blueteamvillage/btv_dc32_badge/art/Camera-1-Edge-01.jpg

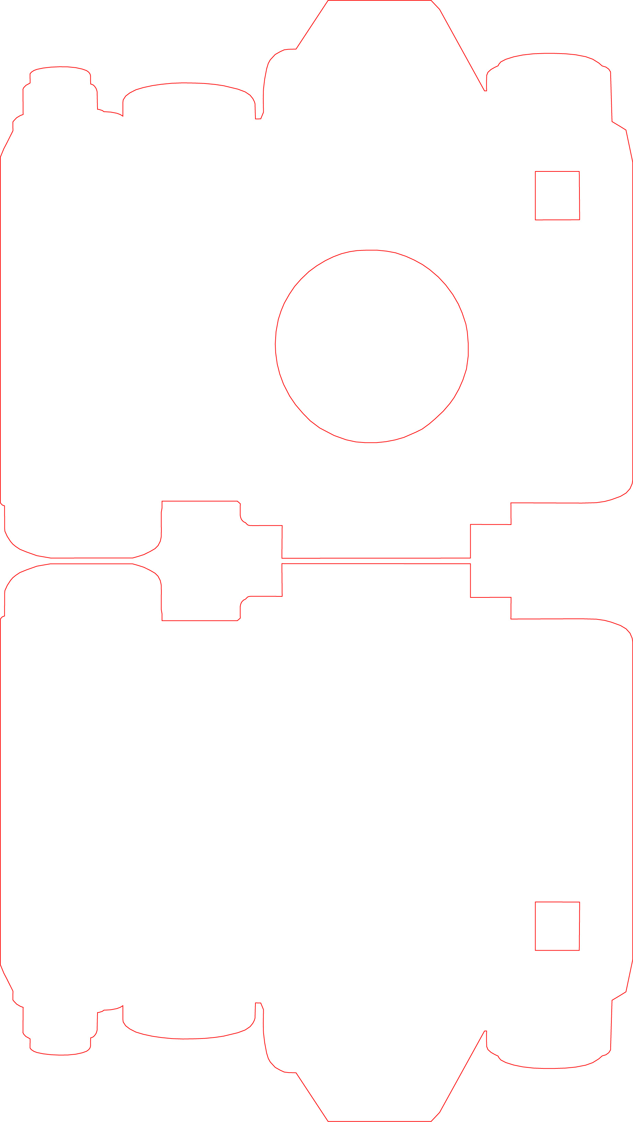
art/Camera-1-Edge-01.jpg
