blueteamvillage/btv_dc32_badge/art/Camera-1-Silk-01.jpg

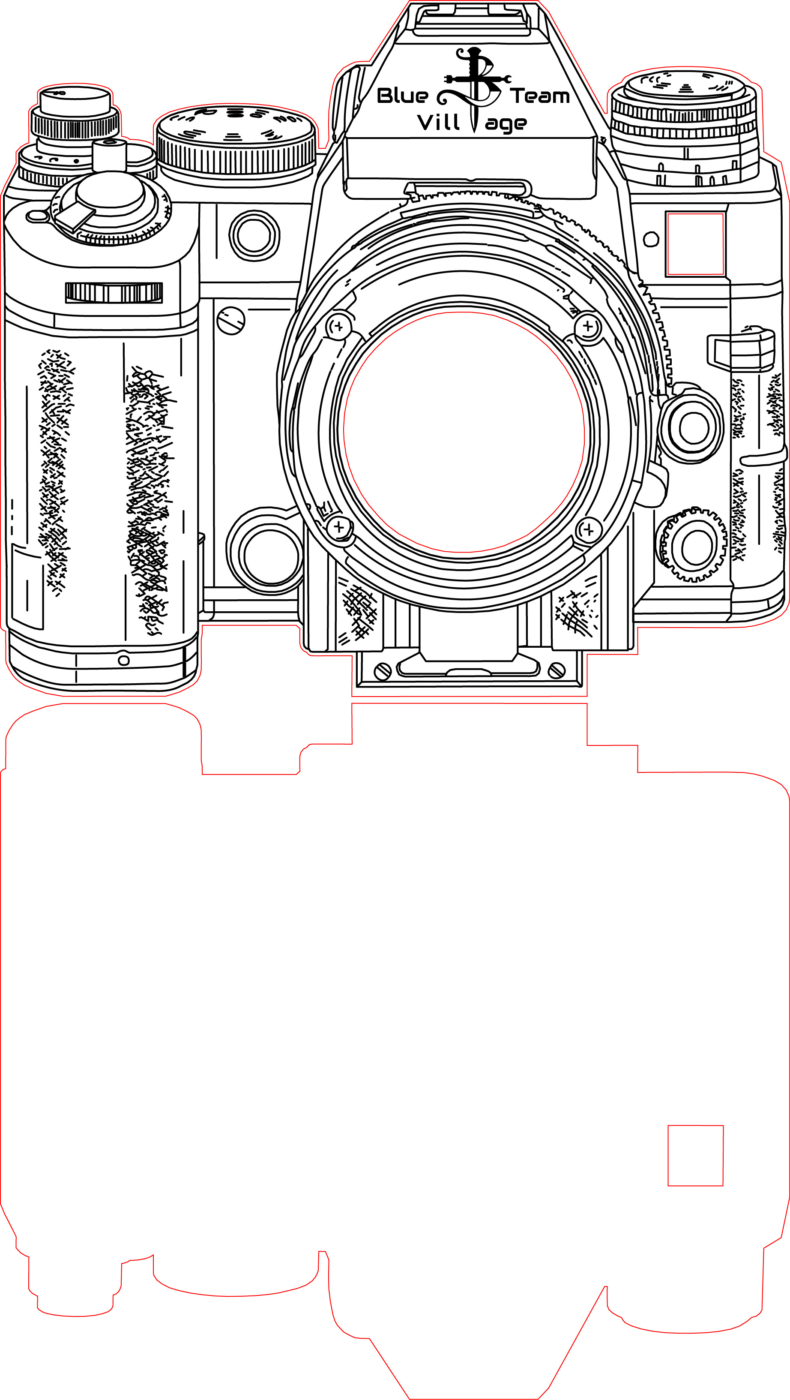
art/Camera-1-Silk-01.jpg
