blueteamvillage/btv_dc32_badge/art/Camera-2-Copper-01.jpg

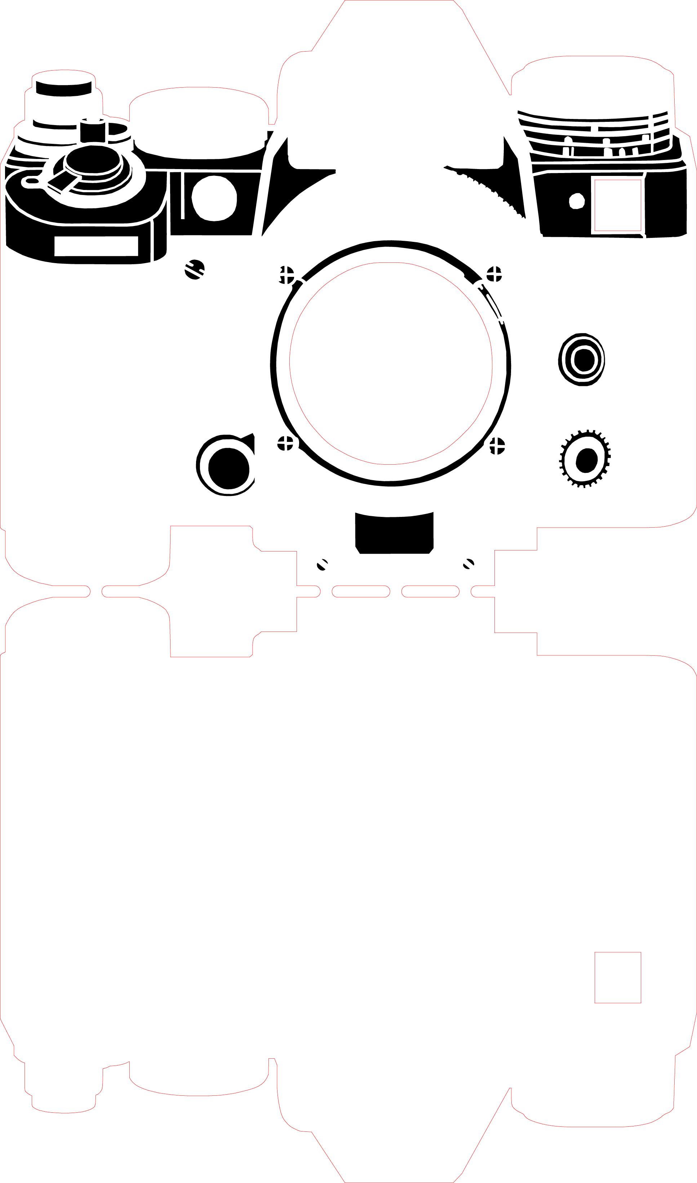
art/Camera-2-Copper-01.jpg
