blueteamvillage/btv_dc32_badge/art/Camera-3-Silk3-01.jpg

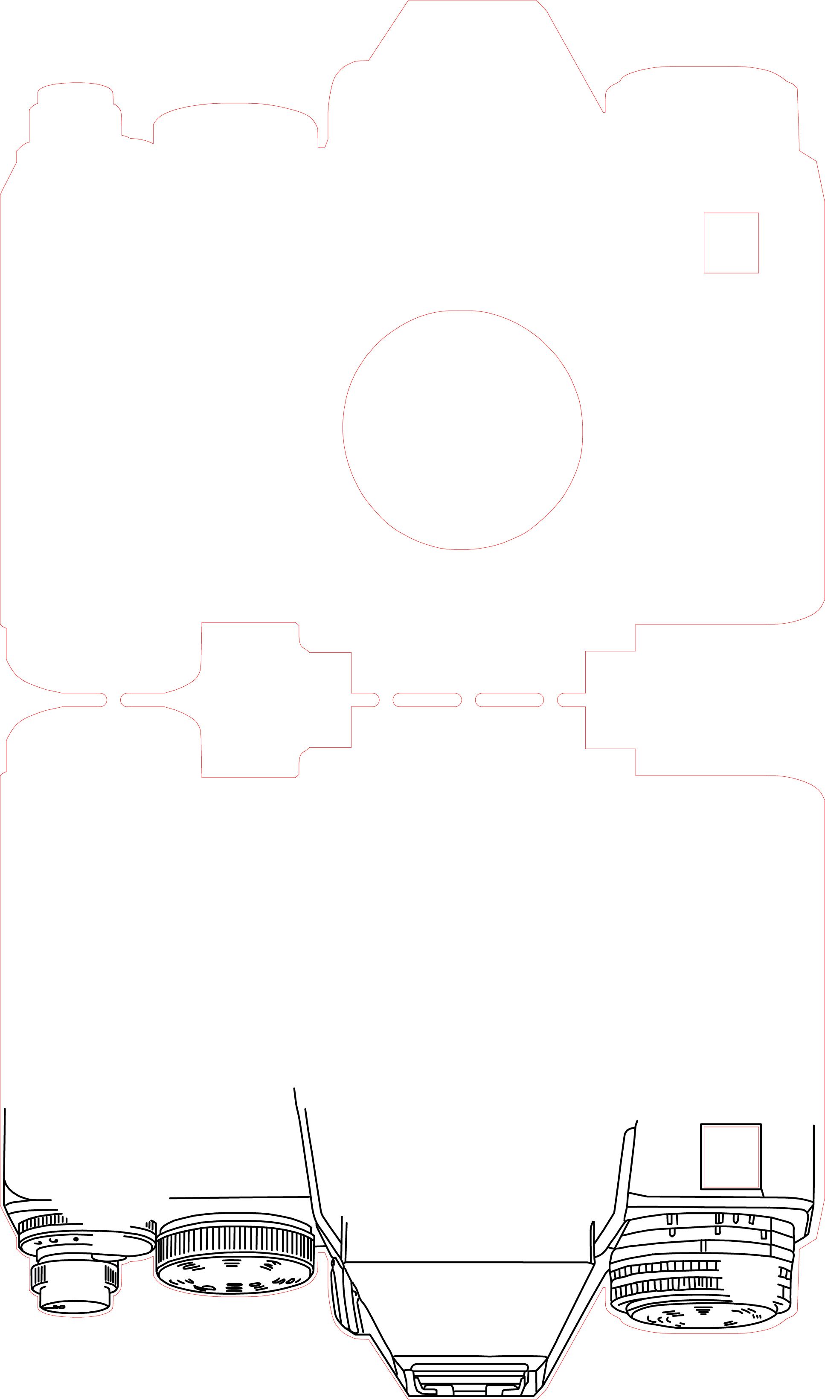
art/Camera-3-Silk3-01.jpg
