blueteamvillage/btv_dc32_badge/art/Camera-4-Silk4-01.jpg

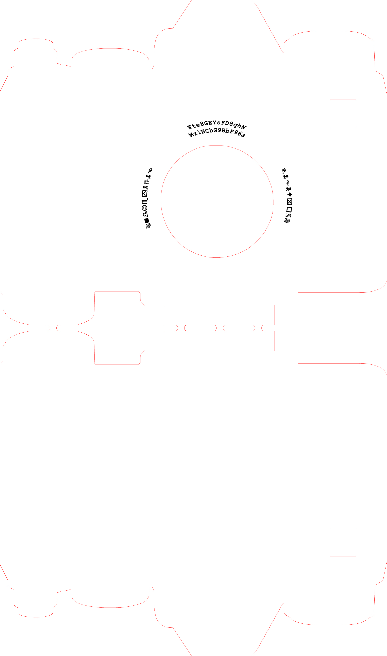
art/Camera-4-Silk4-01.jpg
