blueteamvillage/btv_dc32_badge/art/inspiration/1526_DF_front.webp

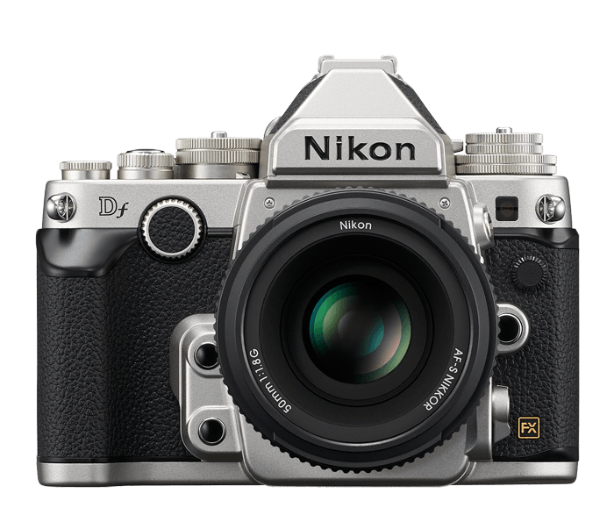
art/inspiration/1526_DF_front.webp
