blueteamvillage/btv_dc32_badge/art/inspiration/alt_bier_steampunk_style_lineart_camera_front_detailed_31d5d3f1-7962-4664-9bf5-ae9651fdb0f0.png

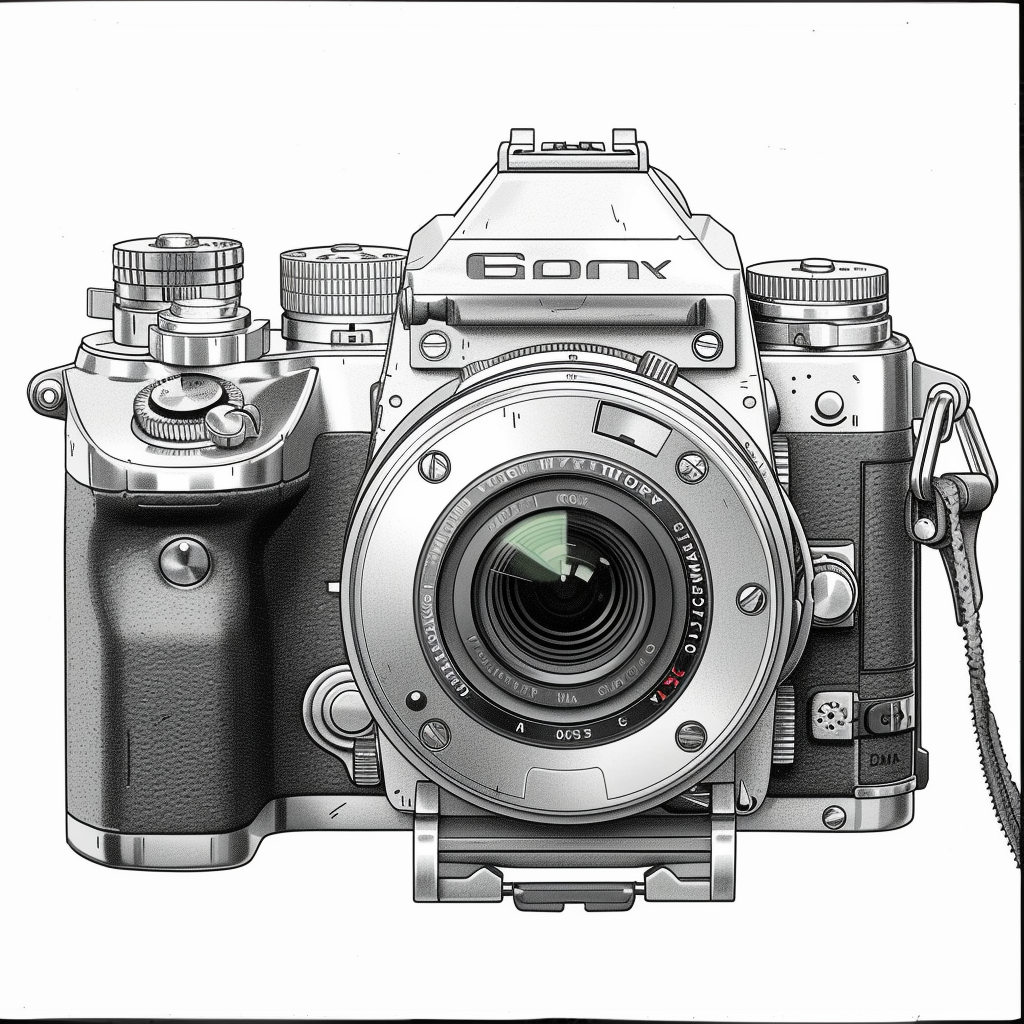
art/inspiration/alt_bier_steampunk_style_lineart_camera_front_detailed_31d5d3f1-7962-4664-9bf5-ae9651fdb0f0.png
