blueteamvillage/btv_dc32_badge/art/inspiration/alt_bier_steampunk_style_lineart_camera_front_detailed_dcd740cc-04af-4e9c-815a-0b84af797cc7.png

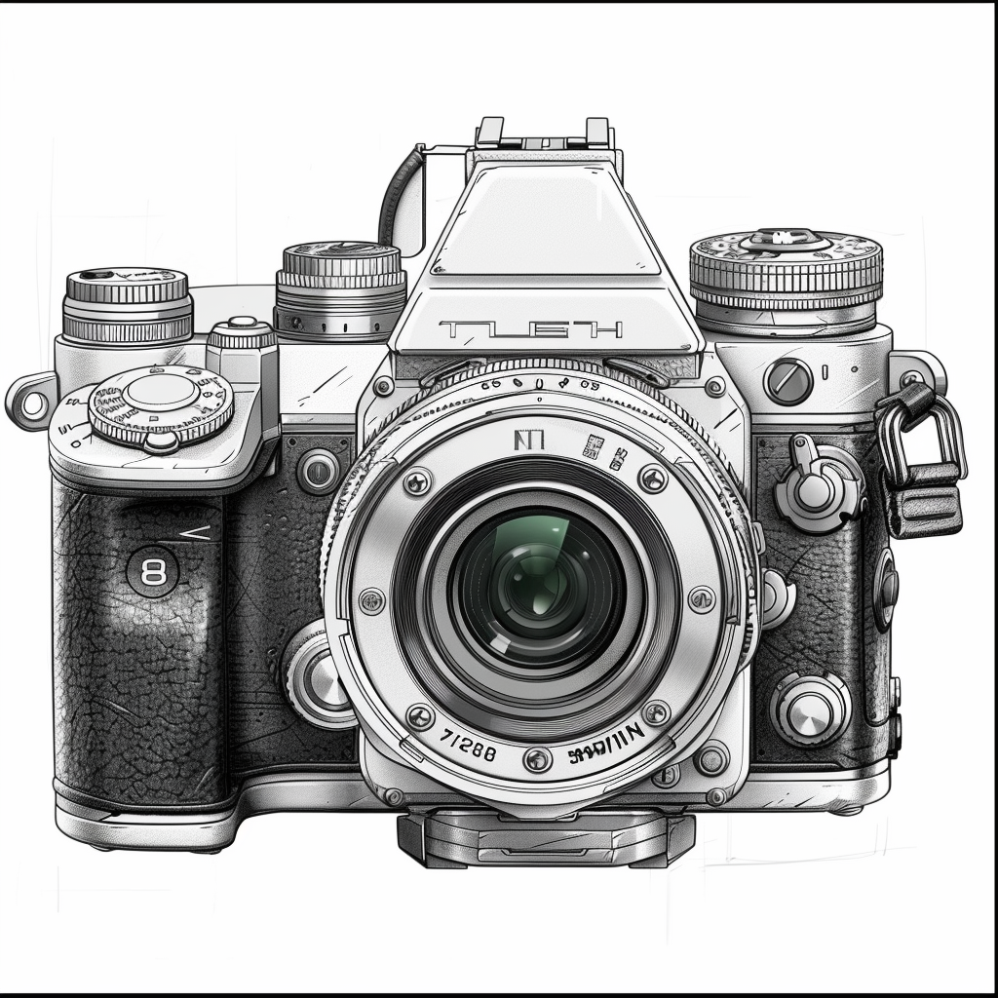
art/inspiration/alt_bier_steampunk_style_lineart_camera_front_detailed_dcd740cc-04af-4e9c-815a-0b84af797cc7.png
