blueteamvillage/btv_dc32_badge/art/inspiration/alt_bier_steampunk_style_lineart_camera_front_detailed_ddf231e1-9c2c-4ddd-9c3d-0c231ffb5367.png

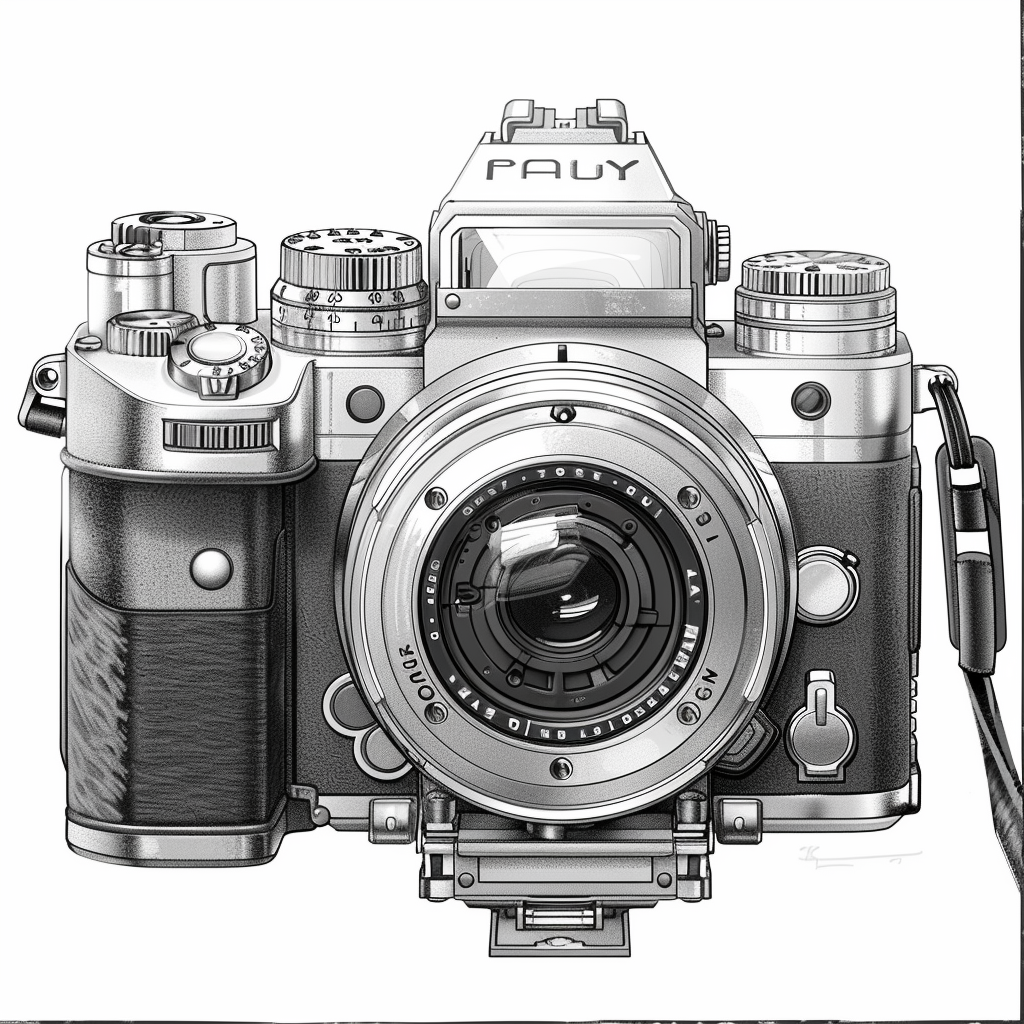
art/inspiration/alt_bier_steampunk_style_lineart_camera_front_detailed_ddf231e1-9c2c-4ddd-9c3d-0c231ffb5367.png
