blueteamvillage/btv_dc32_badge/art/inspiration/camera-with-flashbulb-csa-images.jpg

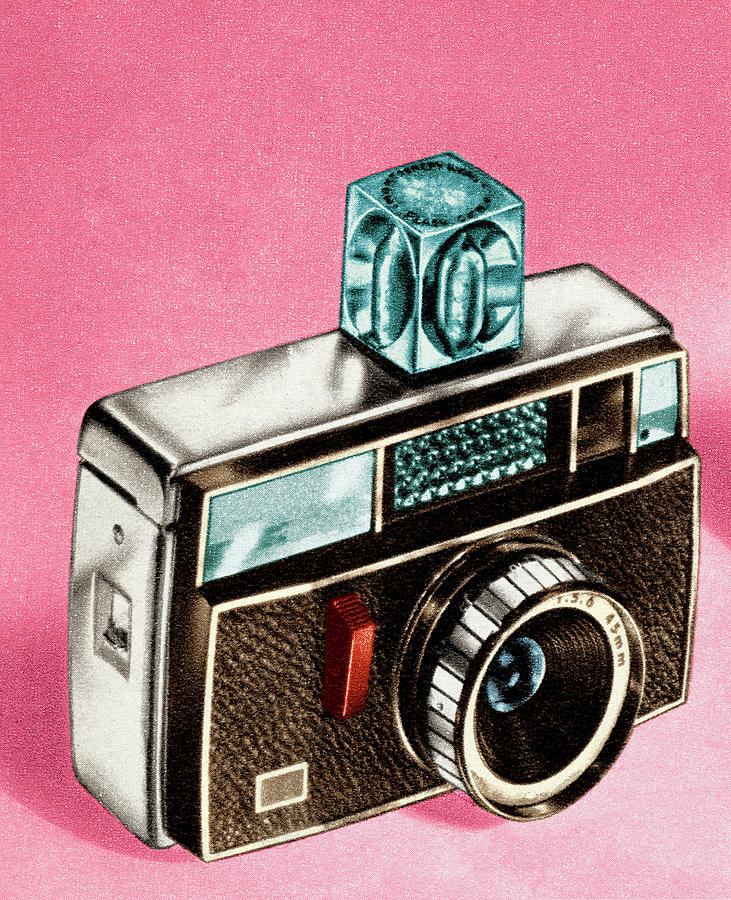
art/inspiration/camera-with-flashbulb-csa-images.jpg
