blueteamvillage/btv_dc32_badge/art/inspiration/il_794xN.4338796224_chcm.webp

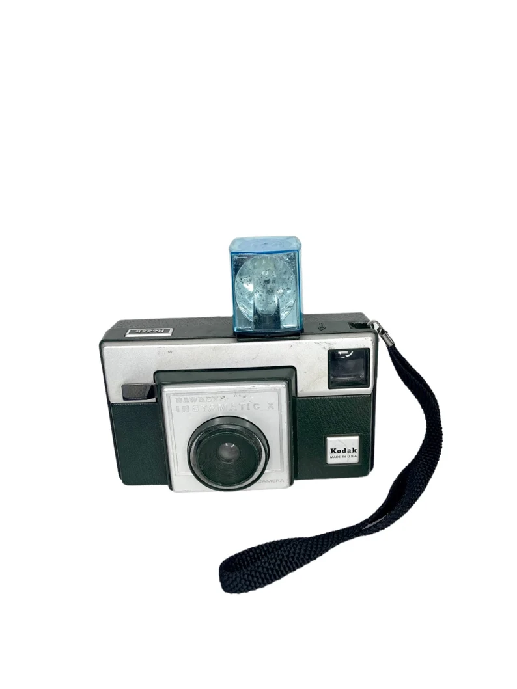
art/inspiration/il_794xN.4338796224_chcm.webp
