blueteamvillage/btv_dc32_badge/art/inspiration/main-qimg-265a1cb40d4eaab294449824ee6765e3-lq.jpeg

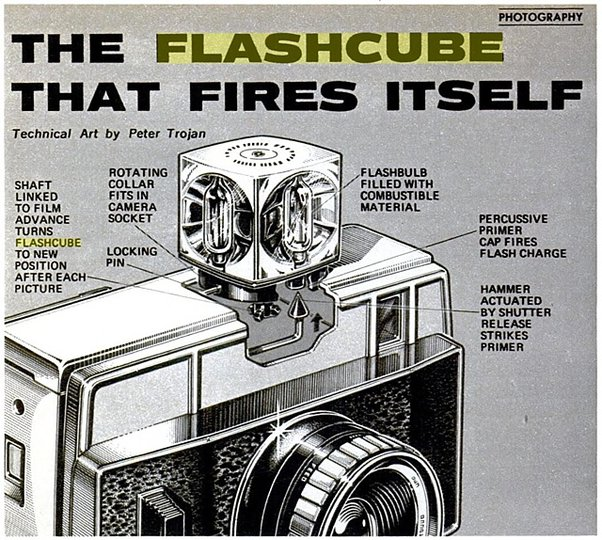
art/inspiration/main-qimg-265a1cb40d4eaab294449824ee6765e3-lq.jpeg
