blueteamvillage/btv_dc32_badge/art/inspiration/nikkon-classic-blk.jpeg

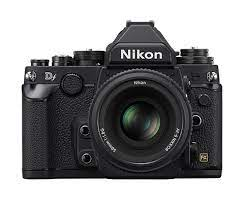
art/inspiration/nikkon-classic-blk.jpeg
