blueteamvillage/btv_dc32_badge/docs/images/ESP32-WeMos-LOLIN32-Lite-pinout-mischianti.png

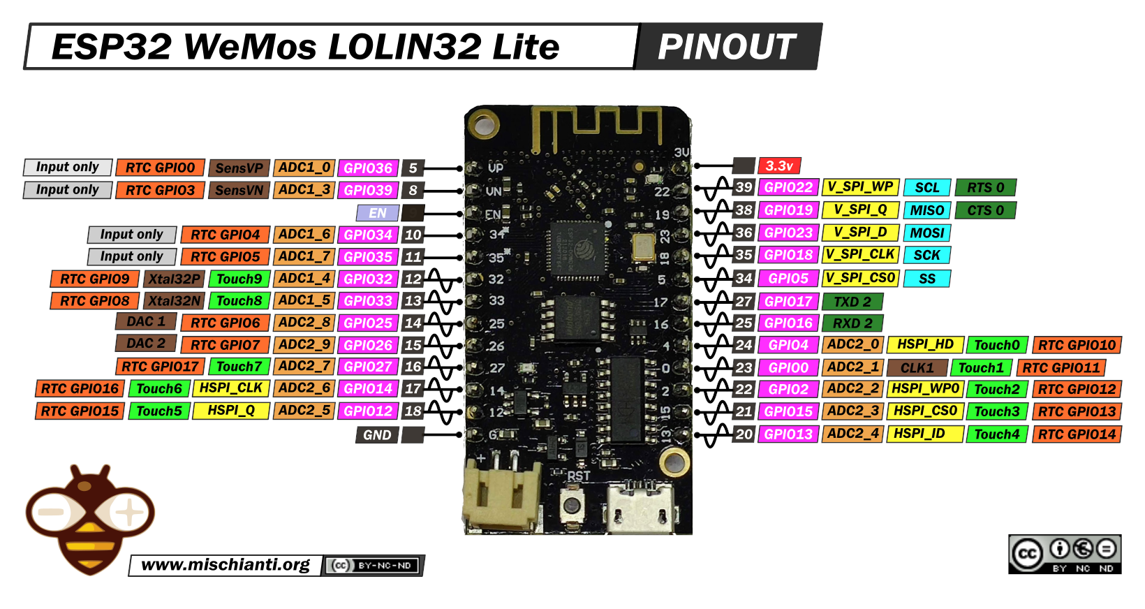
docs/images/ESP32-WeMos-LOLIN32-Lite-pinout-mischianti.png
