blueteamvillage/btv_dc32_badge/eda/camera_badge/3d_models/SW_SS12D00G-Mini-SPDT-Slide-Switch-3pin-1P2T-2-Position-Toggle-Switch-3D.step

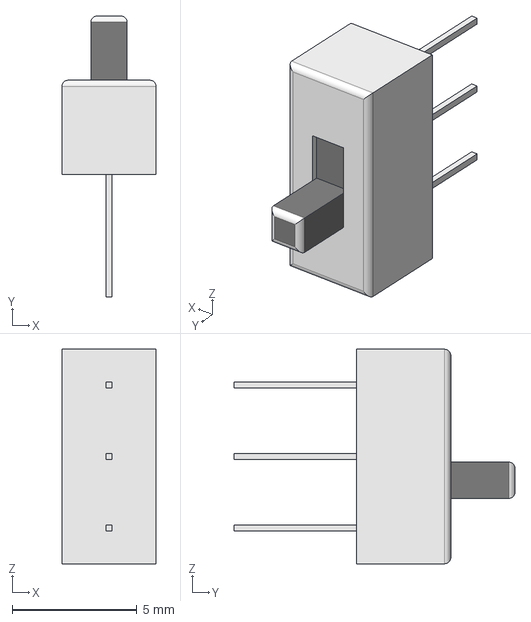
[picture p43: CAD file, 2023-12-28]
eda/camera_badge/3d_models/SW_SS12D00G-Mini-SPDT-Slide-Switch-3pin-1P2T-2-Position-Toggle-Switch-3D.step
3.77 x 11.2 x 8.59 mm
