blueteamvillage/btv_dc32_badge/eda/camera_badge/3d_models/LED_0603_1608Metric.step

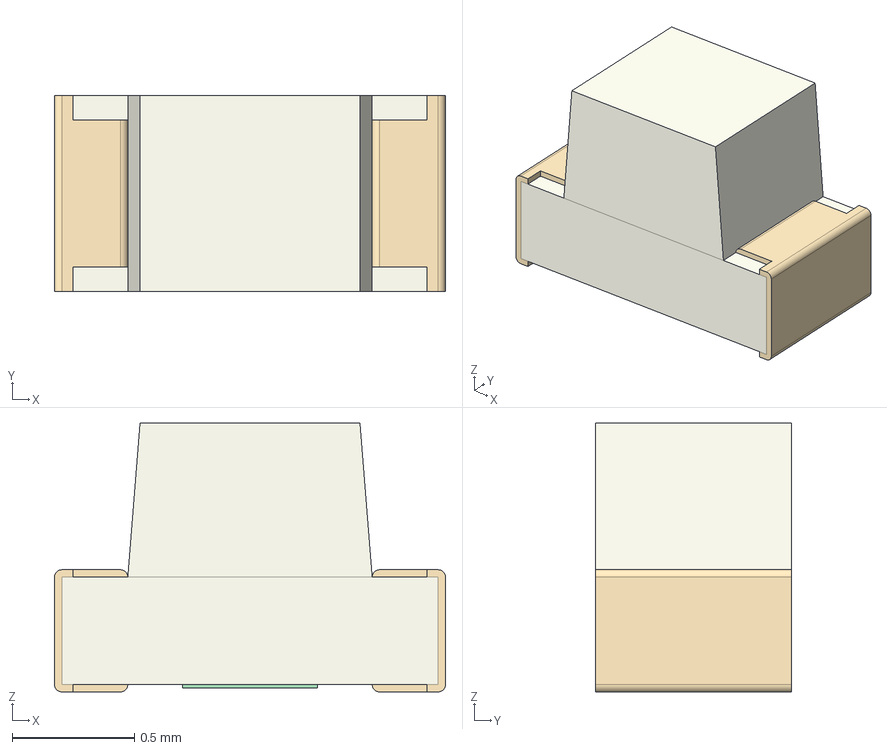
[picture p44: CAD file, 2023-12-28]
eda/camera_badge/3d_models/LED_0603_1608Metric.step
1.60 x 0.8 x 1.10 mm
