blueteamvillage/btv_dc32_badge/eda/camera_badge/3d_models/C_1206_3216Metric.step

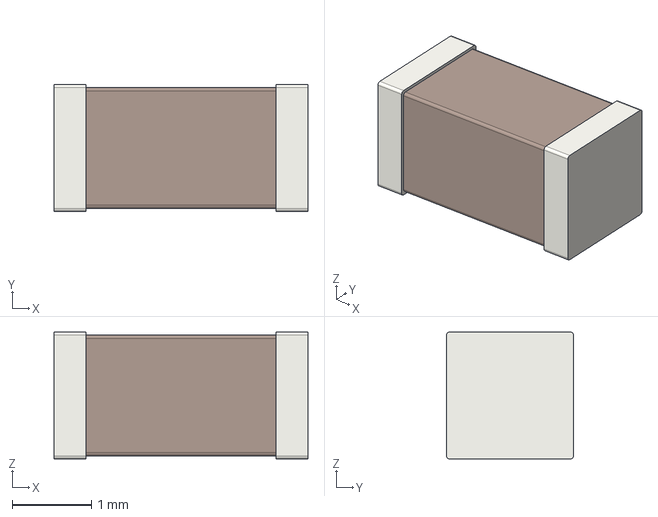
[picture p45: CAD file, 2023-12-28]
eda/camera_badge/3d_models/C_1206_3216Metric.step
3.20 x 1.60 x 1.60 mm
