blueteamvillage/btv_dc32_badge/eda/camera_badge/3d_models/LED_D8.0mm.step

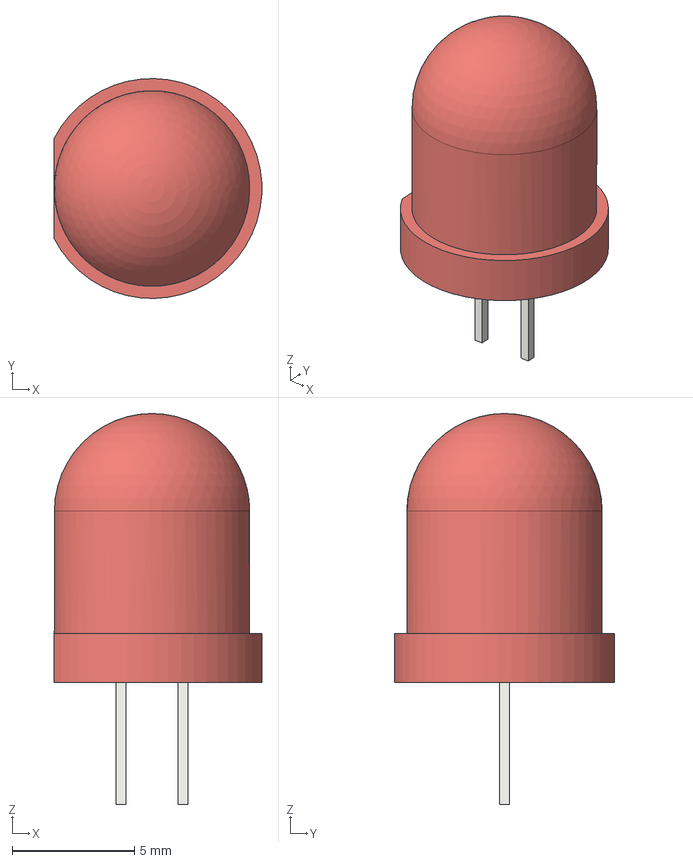
[picture p48: CAD file, 2023-12-28]
eda/camera_badge/3d_models/LED_D8.0mm.step
8.49 x 9.00 x 16.0 mm
