blueteamvillage/btv_dc32_badge/eda/camera_badge/3d_models/PinHeader_1x15_P2.54mm_Vertical.step

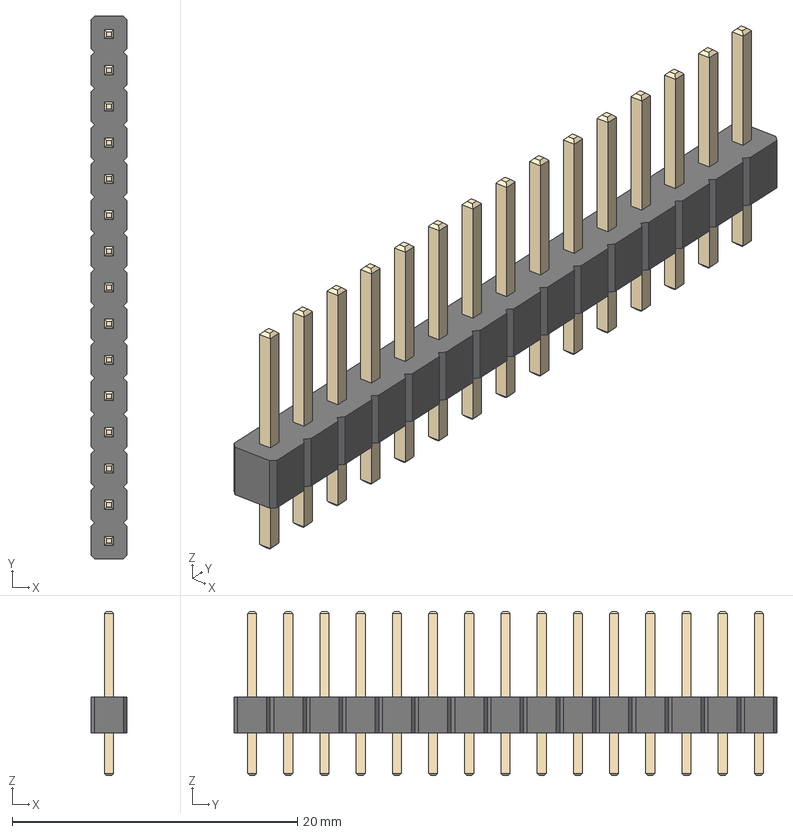
[picture p51: CAD file, 2023-12-28]
eda/camera_badge/3d_models/PinHeader_1x15_P2.54mm_Vertical.step
2.54 x 38.1 x 11.5 mm
