blueteamvillage/btv_dc32_badge/eda/camera_badge/3d_models/CUI_PXO7803-500-M-TR.step

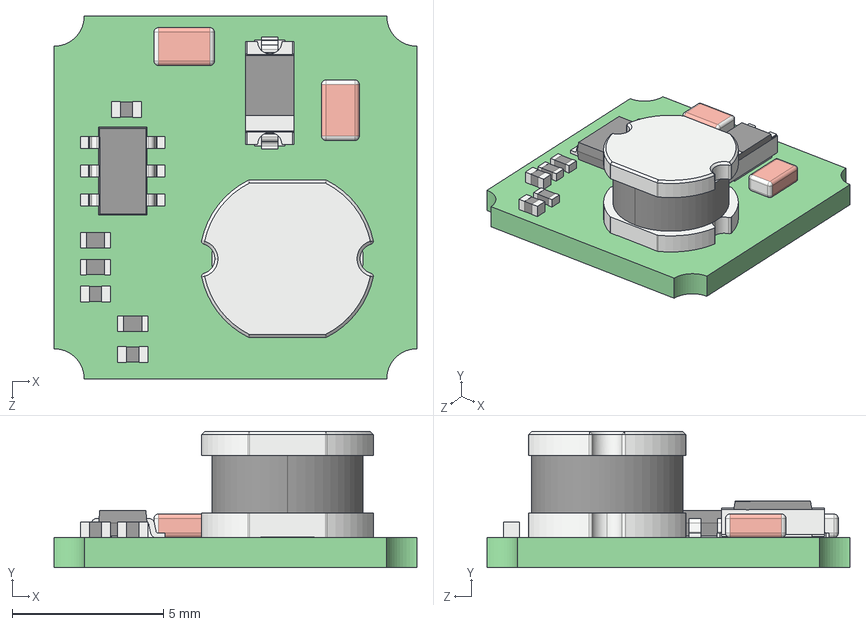
[picture p53: CAD file, 2023-12-28]
eda/camera_badge/3d_models/CUI_PXO7803-500-M-TR.step
12.0 x 4.50 x 12.0 mm
