blueteamvillage/btv_dc32_badge/eda/camera_badge/3d_models/C_Rect_L4.6mm_W2.0mm_P2.50mm_MKS02_FKP02.step

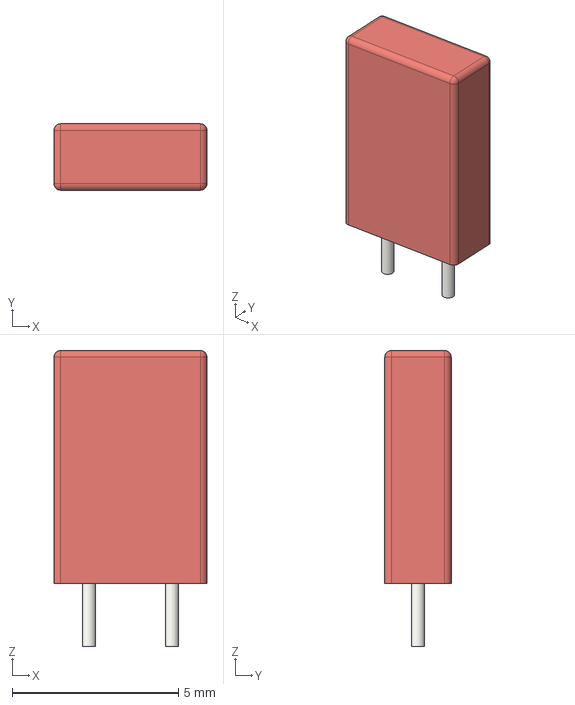
[picture p54: CAD file, 2023-12-28]
eda/camera_badge/3d_models/C_Rect_L4.6mm_W2.0mm_P2.50mm_MKS02_FKP02.step
4.60 x 2.00 x 8.90 mm
