blueteamvillage/btv_dc32_badge/eda/camera_badge/3d_models/TO-92_Inline.step

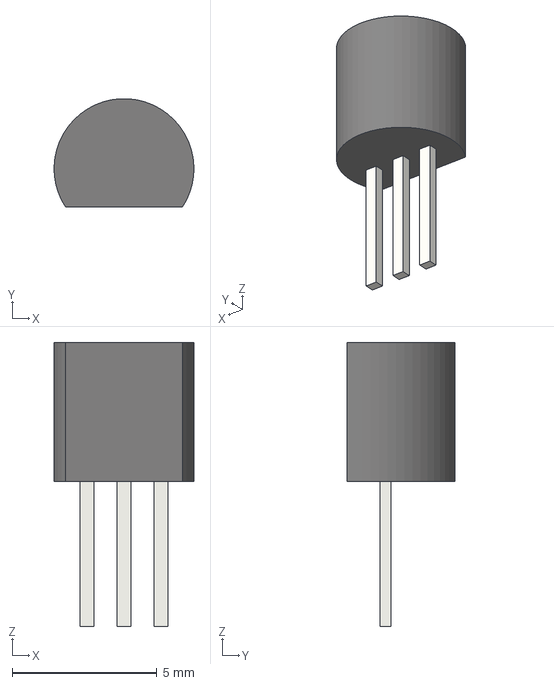
[picture p55: CAD file, 2023-12-28]
eda/camera_badge/3d_models/TO-92_Inline.step
4.83 x 3.74 x 9.80 mm
