blueteamvillage/btv_dc32_badge/eda/camera_badge/3d_models/TS2306A.step

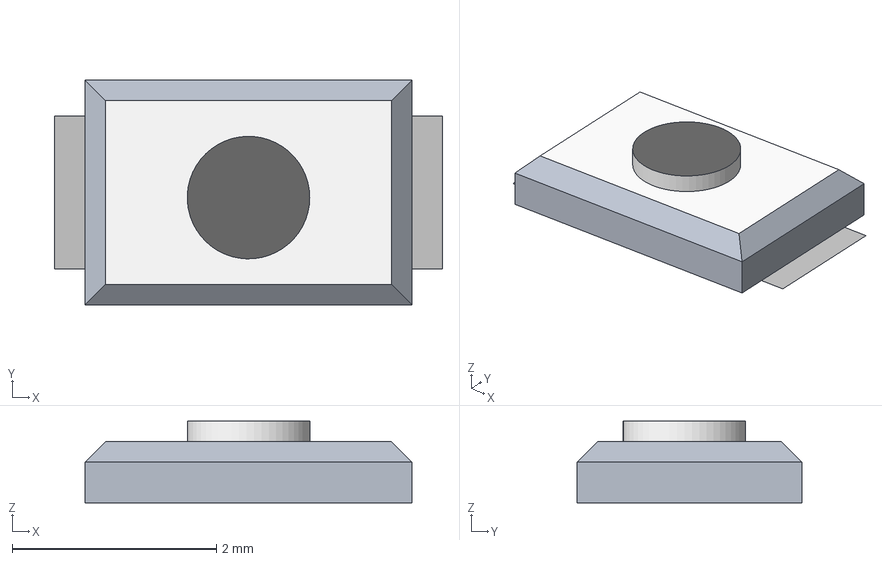
[picture p56: CAD file, 2023-12-28]
eda/camera_badge/3d_models/TS2306A.step
3.80 x 2.20 x 0.8 mm
Plane
