blueteamvillage/btv_dc32_badge/eda/camera_badge/3d_models/BatteryHolder_2466_1xAAA.step

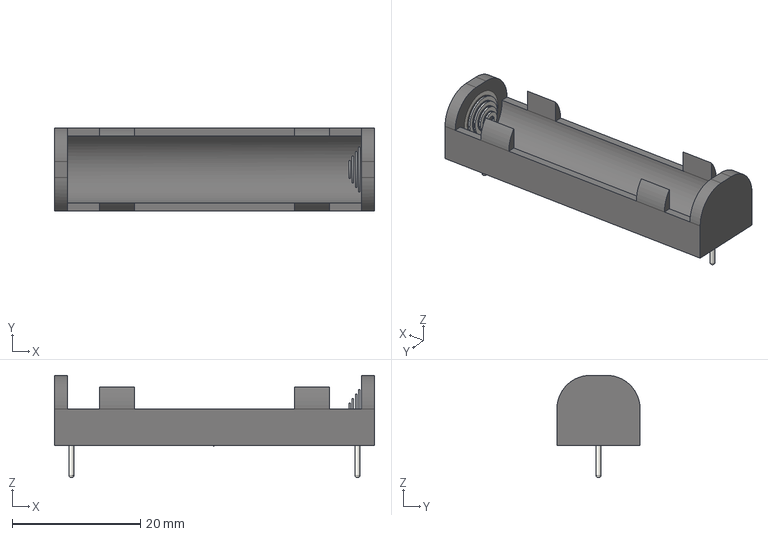
[picture p59: CAD file, 2023-12-28]
eda/camera_badge/3d_models/BatteryHolder_2466_1xAAA.step
50.0 x 13.0 x 16.0 mm
