blueteamvillage/btv_dc32_badge/eda/camera_badge/3d_models/C_Disc_D3.0mm_W2.0mm_P2.50mm.step

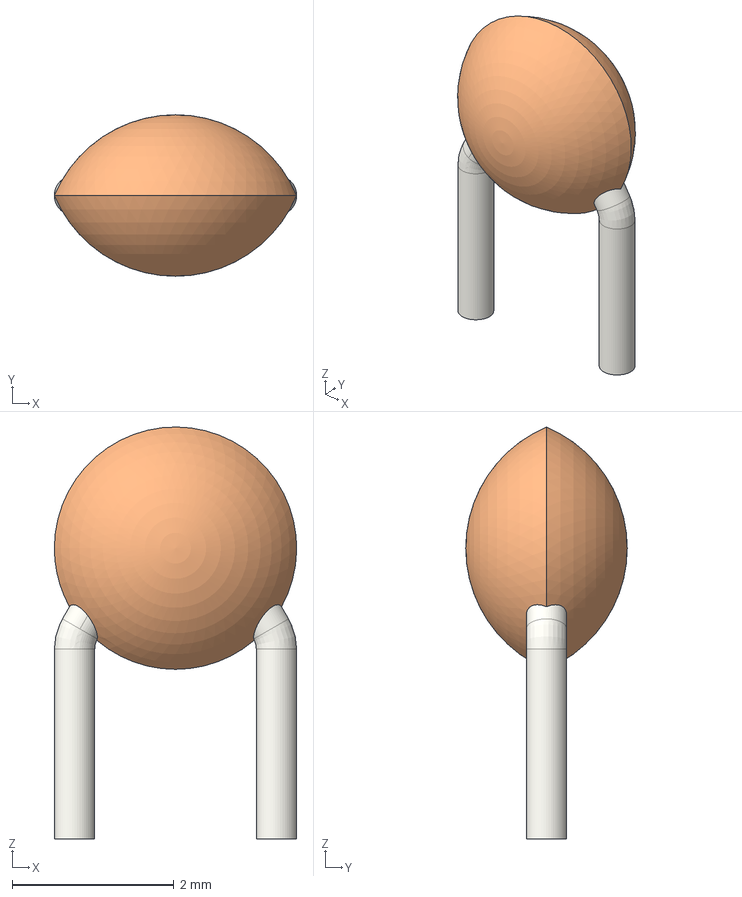
[picture p62: CAD file, 2023-12-28]
eda/camera_badge/3d_models/C_Disc_D3.0mm_W2.0mm_P2.50mm.step
3.00 x 2.00 x 5.10 mm
