blueteamvillage/btv_dc32_badge/eda/camera_badge/3d_models/PinSocket_1x20_P2.54mm_Horizontal.step

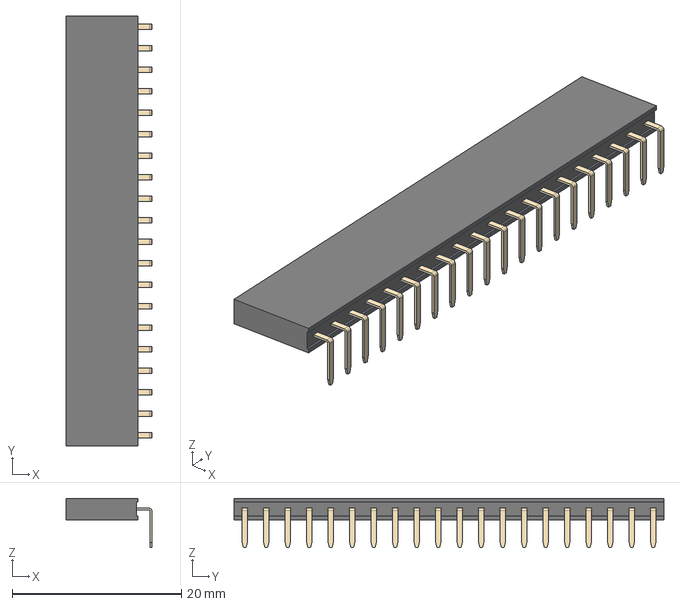
[picture p63: CAD file, 2023-12-28]
eda/camera_badge/3d_models/PinSocket_1x20_P2.54mm_Horizontal.step
10.1 x 50.8 x 5.84 mm
