blueteamvillage/btv_dc32_badge/eda/camera_badge/3d_models/R_1206_3216Metric.step

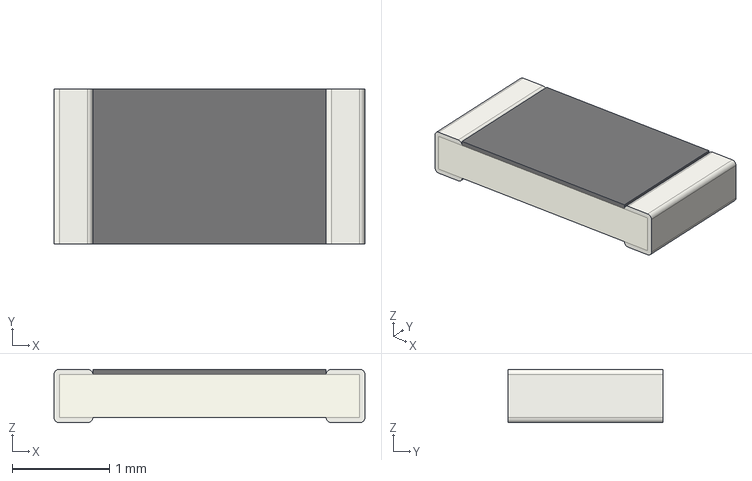
[picture p65: CAD file, 2023-12-28]
eda/camera_badge/3d_models/R_1206_3216Metric.step
3.20 x 1.60 x 0.55 mm
