blueteamvillage/btv_dc32_badge/eda/camera_badge/3d_models/USB_Micro-B_Molex_47346-0001.step

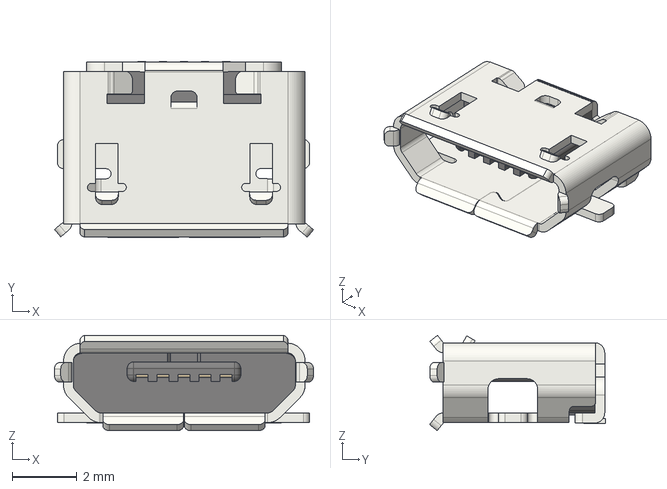
[picture p66: CAD file, 2023-12-28]
eda/camera_badge/3d_models/USB_Micro-B_Molex_47346-0001.step
7.98 x 5.42 x 2.94 mm
