blueteamvillage/btv_dc32_badge/eda/camera_badge/3d_models/PinSocket_1x10_P2.54mm_Horizontal.step

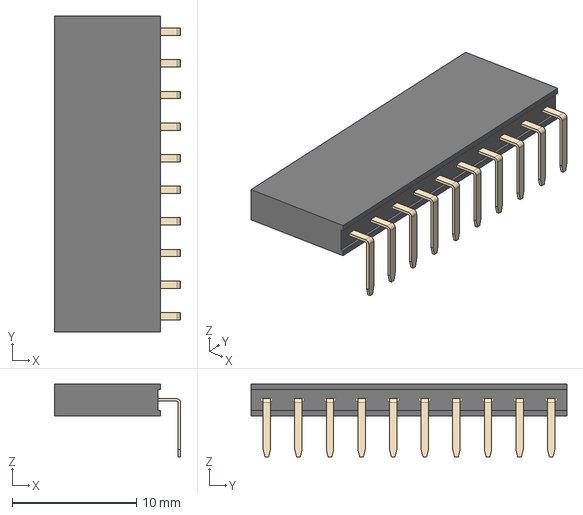
[picture p68: CAD file, 2023-12-28]
eda/camera_badge/3d_models/PinSocket_1x10_P2.54mm_Horizontal.step
10.1 x 25.4 x 5.84 mm
