blueteamvillage/btv_dc32_badge/eda/camera_badge/3d_models/PinSocket_1x10_P2.54mm_Vertical.step

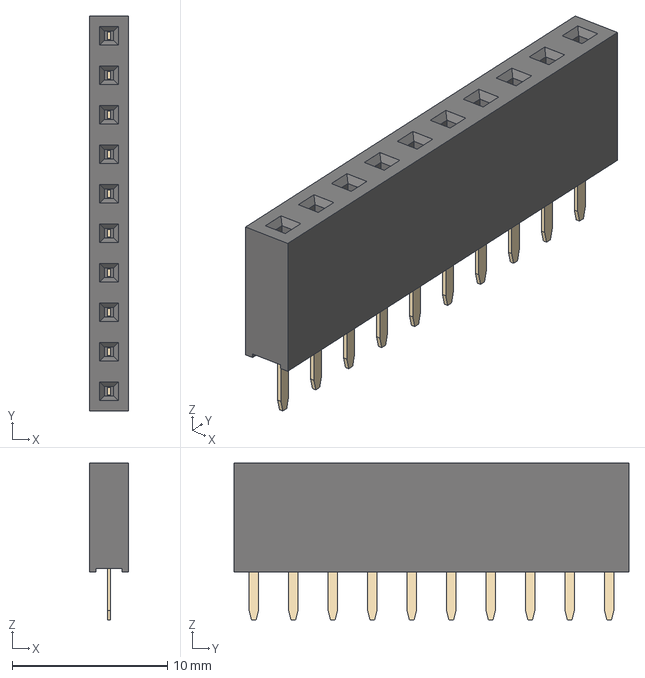
[picture p70: CAD file, 2023-12-28]
eda/camera_badge/3d_models/PinSocket_1x10_P2.54mm_Vertical.step
2.54 x 25.4 x 10.1 mm
