blueteamvillage/btv_dc32_badge/eda/camera_badge/3d_models/Battery_Holder_CR2032_BS-2-1.stp

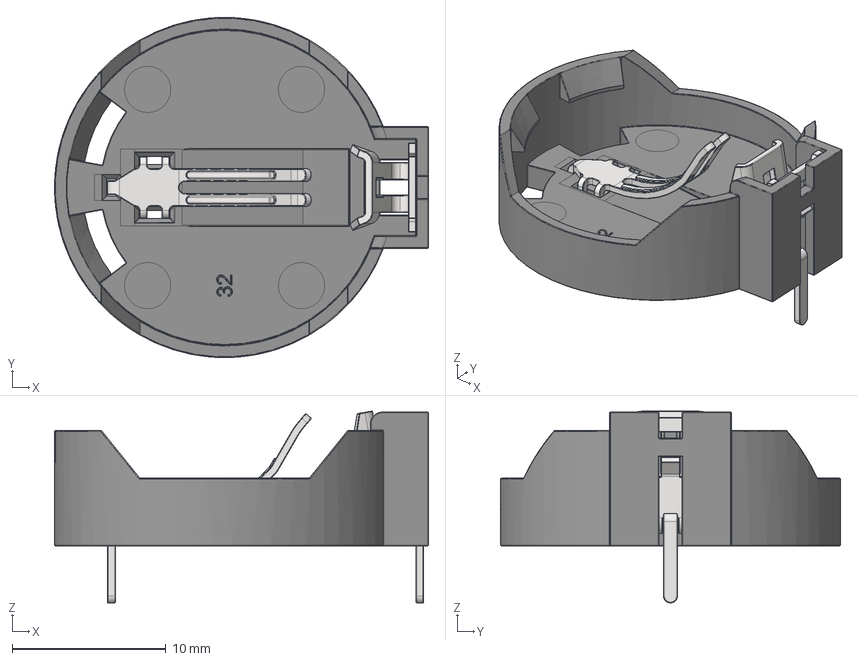
[picture p72: CAD file, 2023-12-28]
eda/camera_badge/3d_models/Battery_Holder_CR2032_BS-2-1.stp
24.3 x 22.1 x 12.5 mm
