blueteamvillage/btv_dc32_badge/eda/camera_badge/3d_models/R_Axial_DIN0207_L6.3mm_D2.5mm_P7.62mm_Horizontal.step

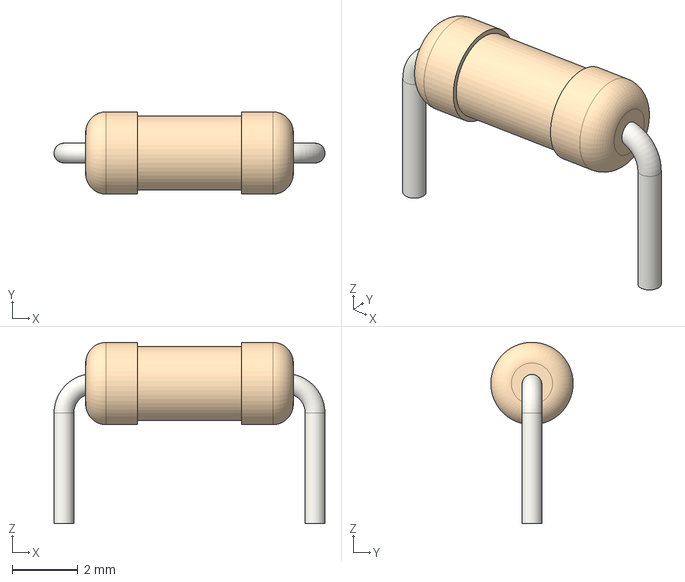
[picture p78: CAD file, 2023-12-28]
eda/camera_badge/3d_models/R_Axial_DIN0207_L6.3mm_D2.5mm_P7.62mm_Horizontal.step
8.22 x 2.50 x 5.50 mm
