blueteamvillage/btv_dc32_badge/eda/camera_badge/3d_models/C_0805_2012Metric.step

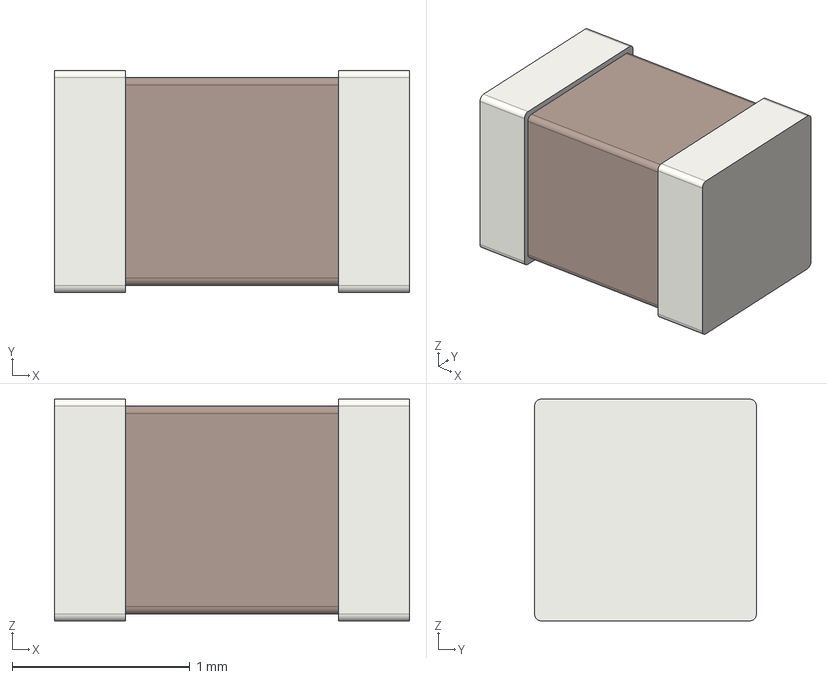
[picture p79: CAD file, 2023-12-28]
eda/camera_badge/3d_models/C_0805_2012Metric.step
2.00 x 1.25 x 1.25 mm
