blueteamvillage/btv_dc32_badge/eda/camera_badge/3d_models/PinSocket_1x05_P2.54mm_Vertical.step

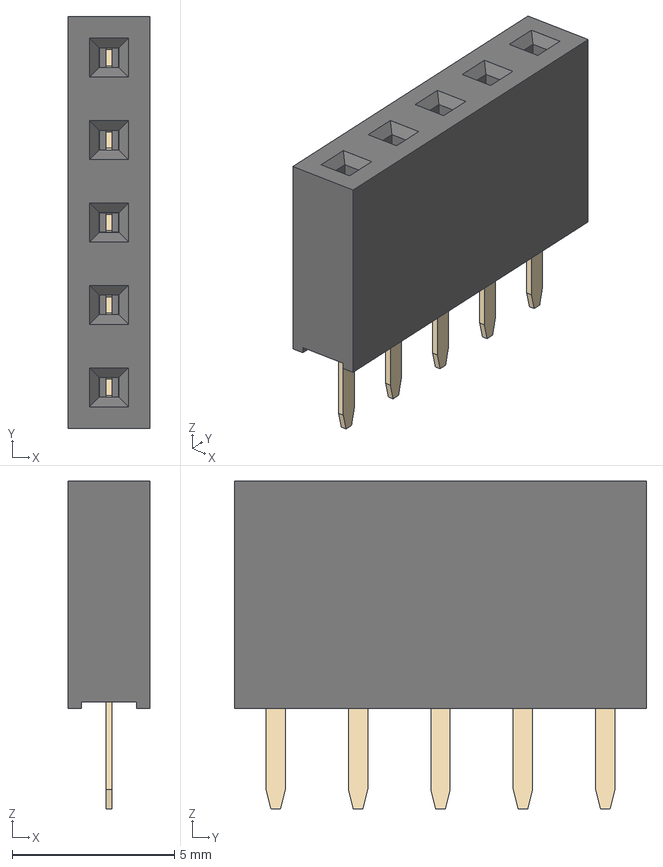
[picture p82: CAD file, 2023-12-28]
eda/camera_badge/3d_models/PinSocket_1x05_P2.54mm_Vertical.step
2.54 x 12.7 x 10.1 mm
