blueteamvillage/btv_dc32_badge/eda/camera_badge/3d_models/RJ45_Amphenol_RJHSE538X.step

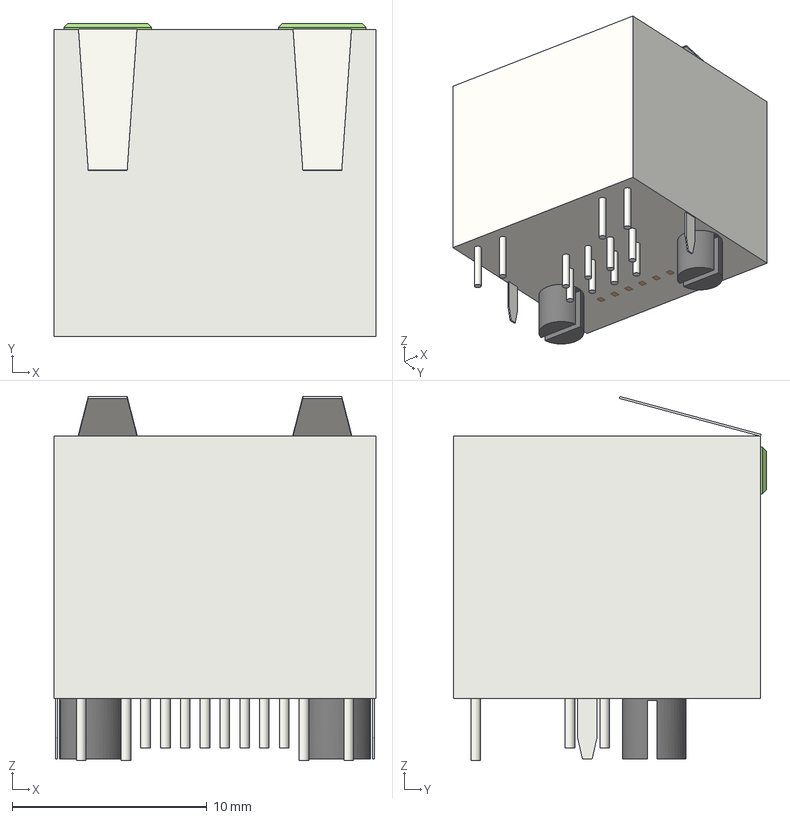
[picture p83: CAD file, 2023-12-28]
eda/camera_badge/3d_models/RJ45_Amphenol_RJHSE538X.step
16.5 x 16.1 x 18.7 mm
