blueteamvillage/btv_dc32_badge/eda/camera_badge/3d_models/RJ45_Amphenol_RJHSE-5080-56544.STEP

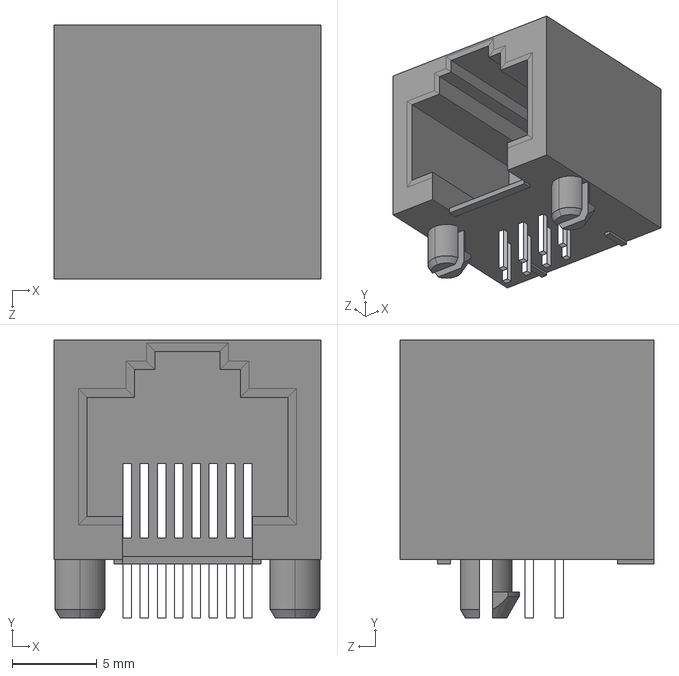
[picture p84: CAD file, 2023-12-28]
eda/camera_badge/3d_models/RJ45_Amphenol_RJHSE-5080-56544.STEP
15.7 x 16.4 x 15.0 mm
