blueteamvillage/btv_dc32_badge/eda/camera_badge/3d_models/R_0603_1608Metric.step

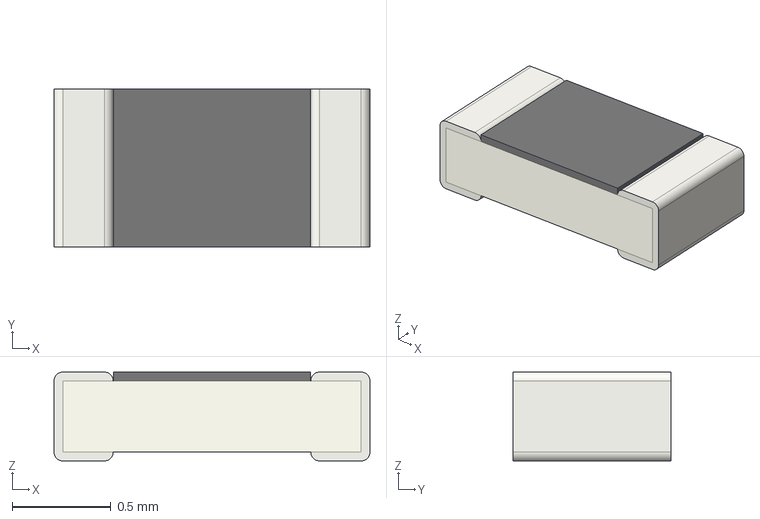
[picture p88: CAD file, 2023-12-28]
eda/camera_badge/3d_models/R_0603_1608Metric.step
1.60 x 0.8 x 0.45 mm
