blueteamvillage/btv_dc32_badge/eda/camera_badge/3d_models/PinHeader_1x01_P2.54mm_Horizontal.step

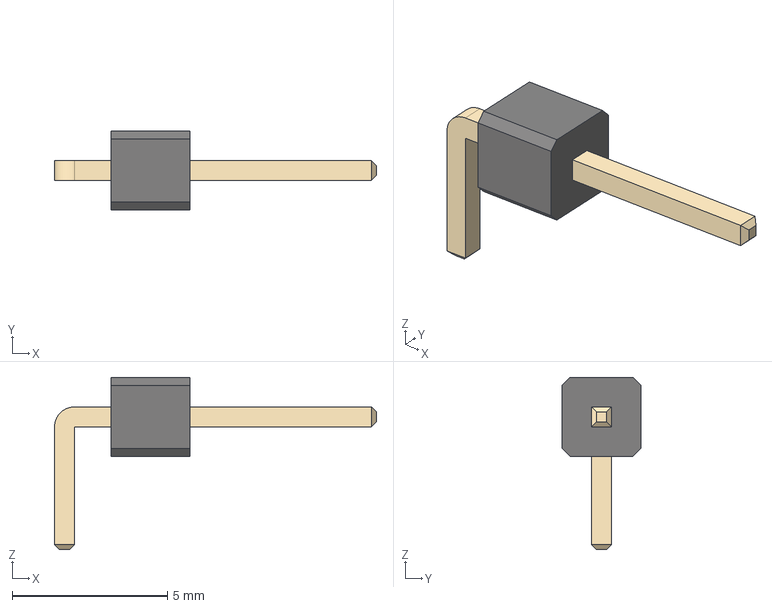
[picture p90: CAD file, 2023-12-28]
eda/camera_badge/3d_models/PinHeader_1x01_P2.54mm_Horizontal.step
10.4 x 2.54 x 5.54 mm
