blueteamvillage/btv_dc32_badge/eda/camera_badge/3d_models/BatteryHolder_2468_2xAAA.step

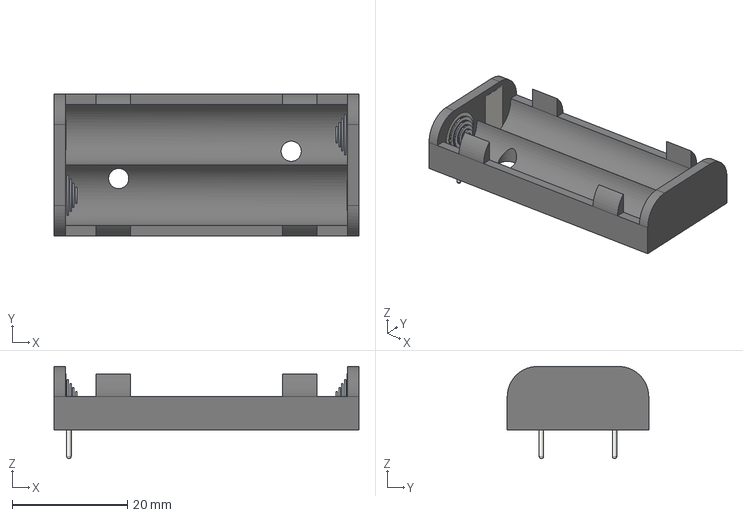
[picture p91: CAD file, 2023-12-28]
eda/camera_badge/3d_models/BatteryHolder_2468_2xAAA.step
53.0 x 24.6 x 16.0 mm
