blueteamvillage/btv_dc32_badge/eda/camera_badge/3d_models/SOT-23.step

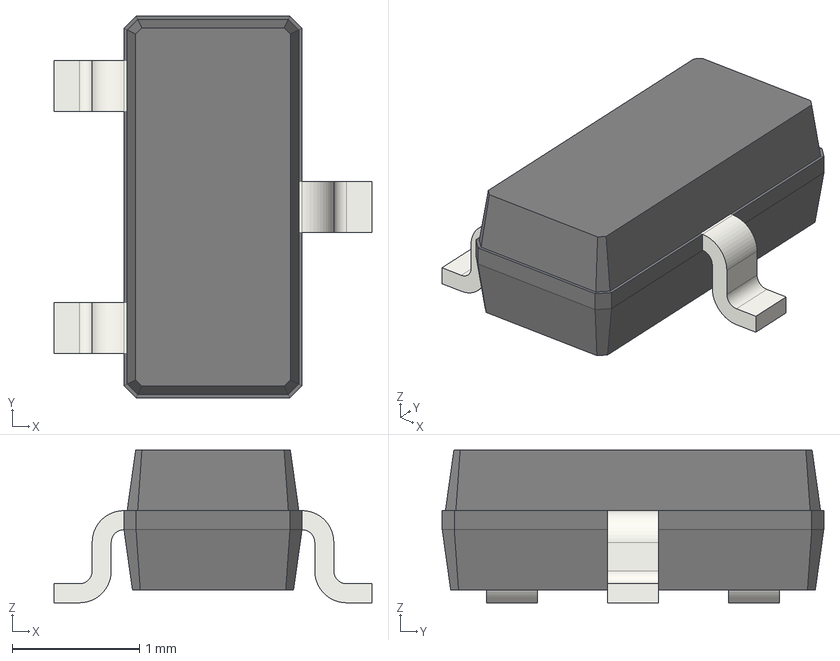
[picture p92: CAD file, 2023-12-28]
eda/camera_badge/3d_models/SOT-23.step
2.50 x 3.00 x 1.20 mm
