blueteamvillage/btv_dc32_badge/eda/camera_badge/3d_models/LED_D5.0mm.step

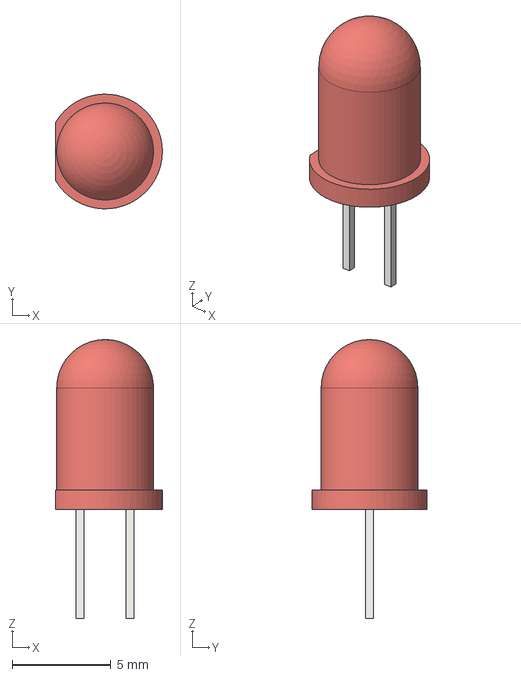
[picture p95: CAD file, 2023-12-28]
eda/camera_badge/3d_models/LED_D5.0mm.step
5.40 x 5.79 x 14.1 mm
