blueteamvillage/btv_dc32_badge/eda/camera_badge/3d_models/Battery_Holder_3xAAA_Simple.step

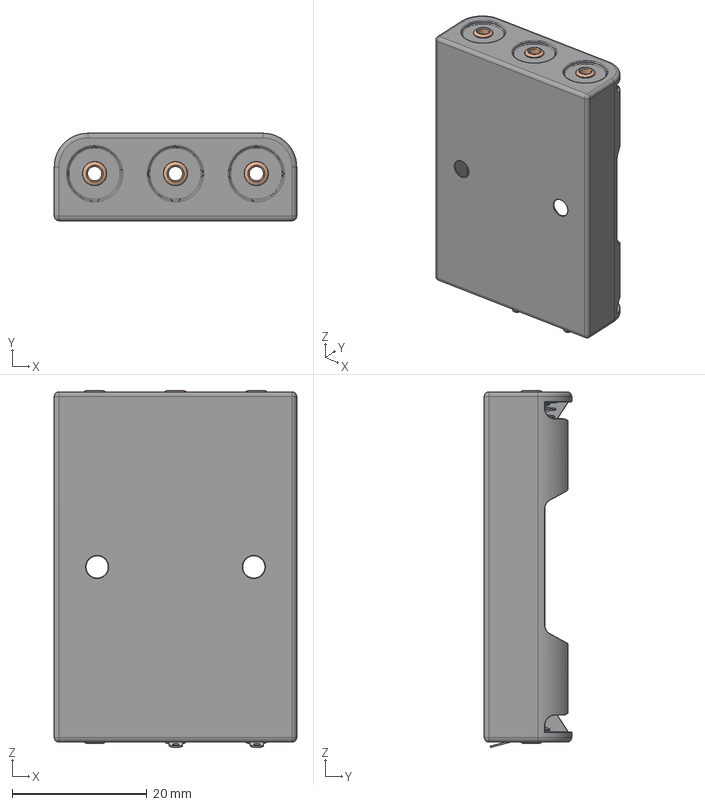
[picture p97: CAD file, 2023-12-28]
eda/camera_badge/3d_models/Battery_Holder_3xAAA_Simple.step
36.0 x 13.0 x 53.0 mm
