blueteamvillage/btv_dc32_badge/eda/camera_badge/3d_models/LED_D3.0mm-3.step

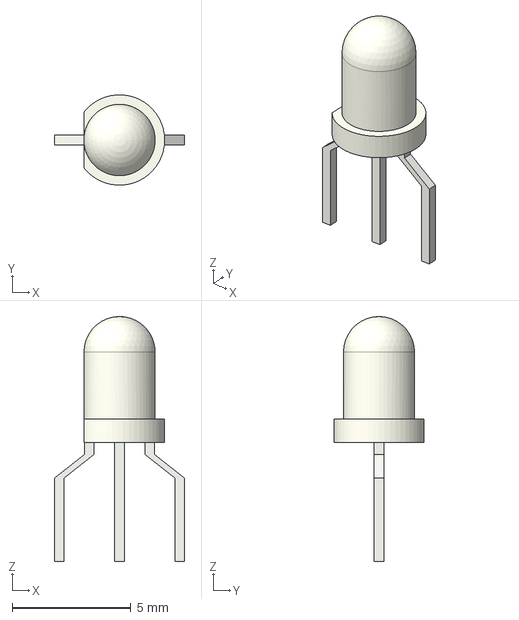
[picture p102: CAD file, 2023-12-28]
eda/camera_badge/3d_models/LED_D3.0mm-3.step
5.48 x 3.80 x 10.3 mm
