blueteamvillage/btv_dc32_badge/eda/camera_badge/3d_models/CP_Radial_D6.3mm_P2.50mm.step

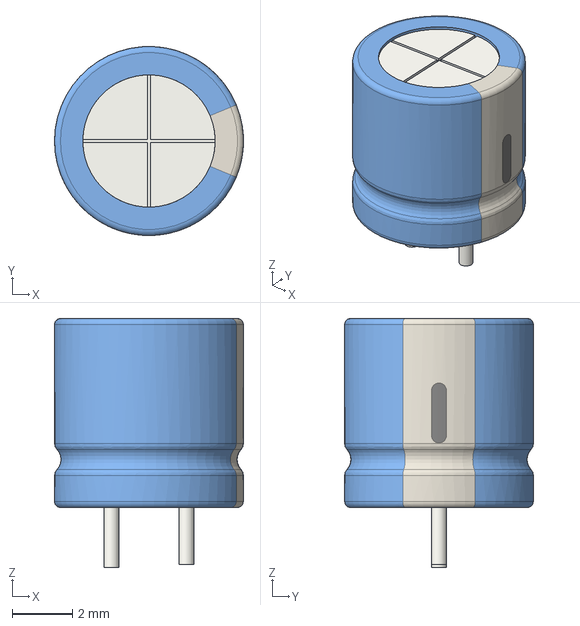
[picture p103: CAD file, 2023-12-28]
eda/camera_badge/3d_models/CP_Radial_D6.3mm_P2.50mm.step
6.30 x 6.30 x 8.30 mm
