blueteamvillage/btv_dc32_badge/eda/camera_badge/3d_models/PinHeader_1x09_P2.54mm_Horizontal.step

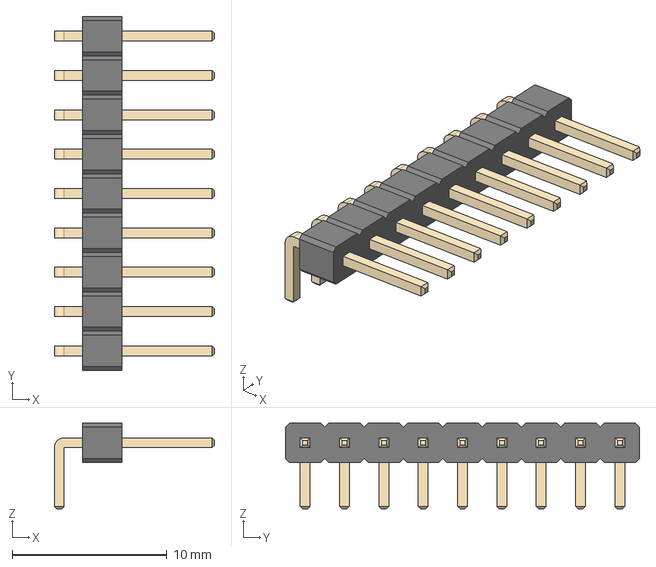
[picture p106: CAD file, 2023-12-28]
eda/camera_badge/3d_models/PinHeader_1x09_P2.54mm_Horizontal.step
10.4 x 22.9 x 5.54 mm
