blueteamvillage/btv_dc32_badge/eda/camera_badge/3d_models/LED_D3.0mm.step

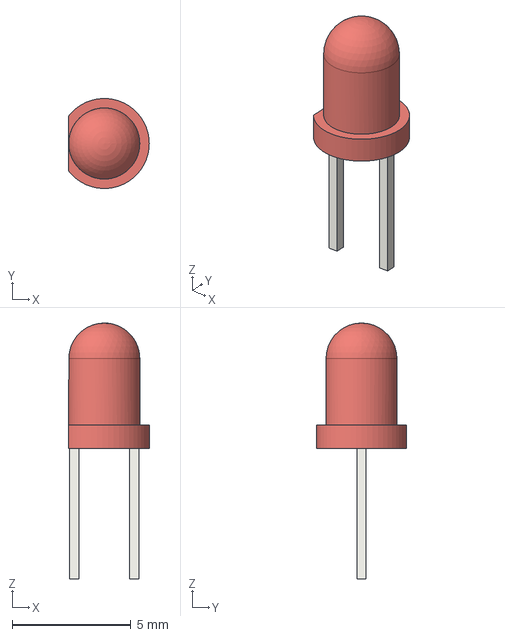
[picture p109: CAD file, 2023-12-28]
eda/camera_badge/3d_models/LED_D3.0mm.step
3.40 x 3.80 x 10.8 mm
